matoushybl/breathe/firmware/src/lib.rs

#![no_std]

pub mod rendering;
pub mod scd30;
pub mod usb_parser;

use core::sync::atomic::{AtomicUsize, Ordering};

use defmt_rtt as _; // global logger
use panic_probe as _;
use stm32f4xx_hal as _; // memory layout

#[defmt::timestamp]
fn timestamp() -> u64 {
    static COUNT: AtomicUsize = AtomicUsize::new(0);
    // NOTE(no-CAS) `timestamps` runs with interrupts disabled
    let n = COUNT.load(Ordering::Relaxed);
    COUNT.store(n + 1, Ordering::Relaxed);
    n as u64
}

/// Terminates the application and makes `probe-run` exit with exit-code = 0
pub fn exit() -> ! {
    loop {
        cortex_m::asm::bkpt();
    }
}
